ccadic/openDTU-Sulfuroid/finalbox3.JPG

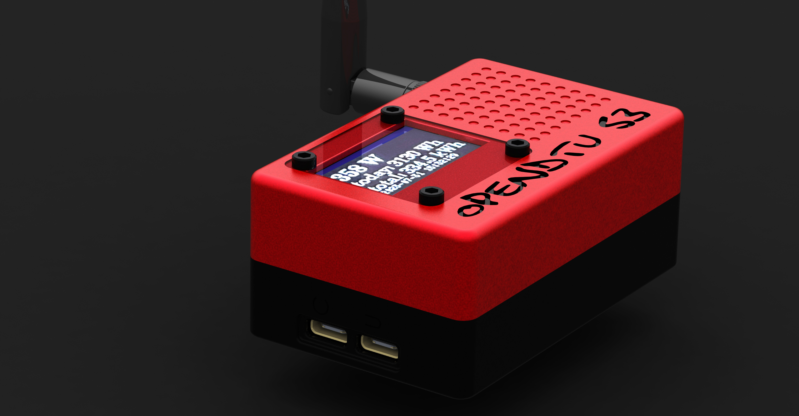
finalbox3.JPG
