ccadic/openDTU-Sulfuroid/finalbox4.JPG

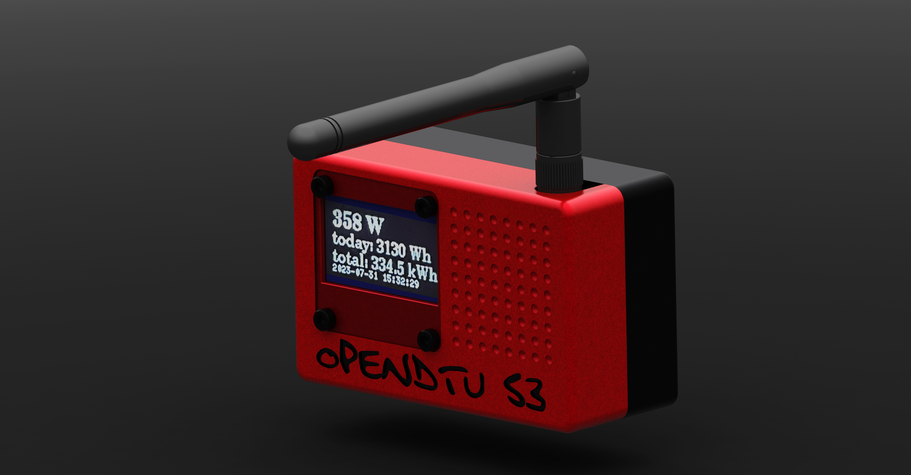
finalbox4.JPG
