ccadic/openDTU-Sulfuroid/openDTU3.jpg

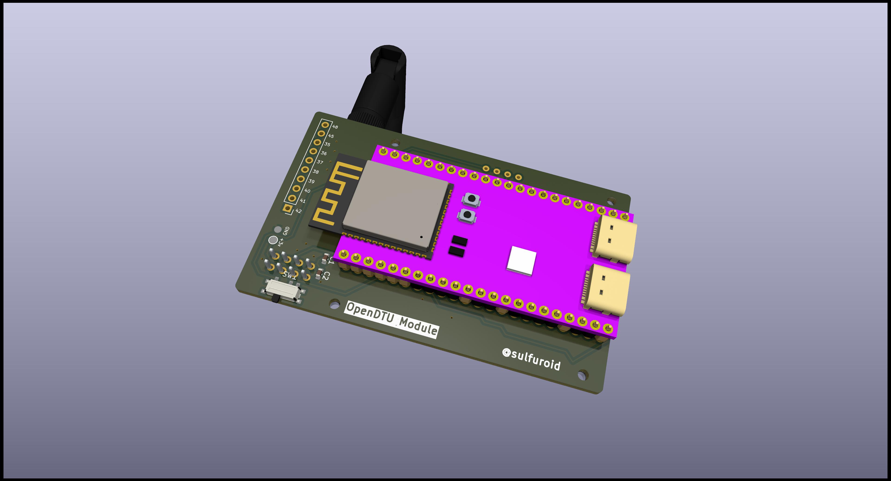
openDTU3.jpg
