ccadic/openDTU-Sulfuroid/openDTU.jpg

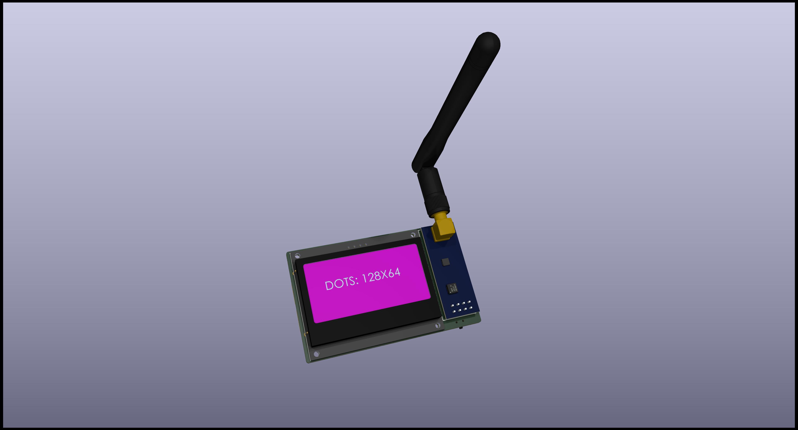
openDTU.jpg
