ccadic/openDTU-Sulfuroid/openDTUBIG6.JPG

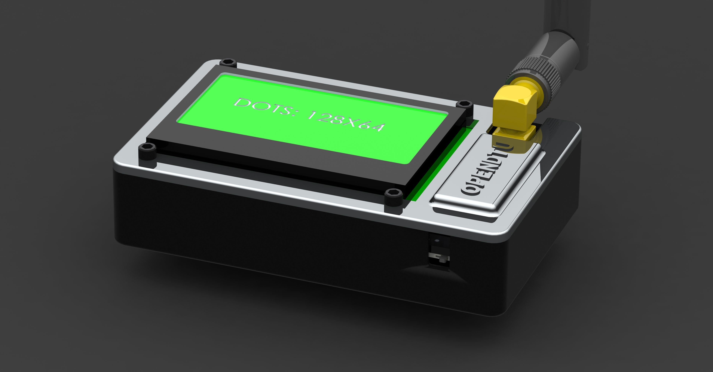
openDTUBIG6.JPG
