ccadic/openDTU-Sulfuroid/Untitled2.JPG

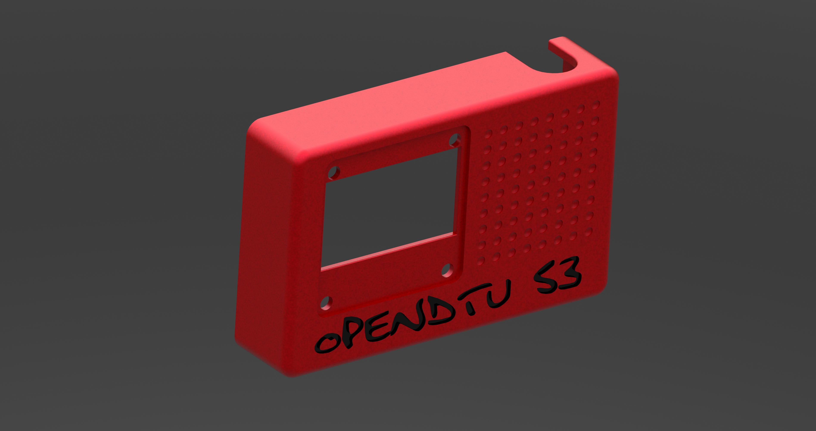
Untitled2.JPG
