ccadic/openDTU-Sulfuroid/Untitled.JPG

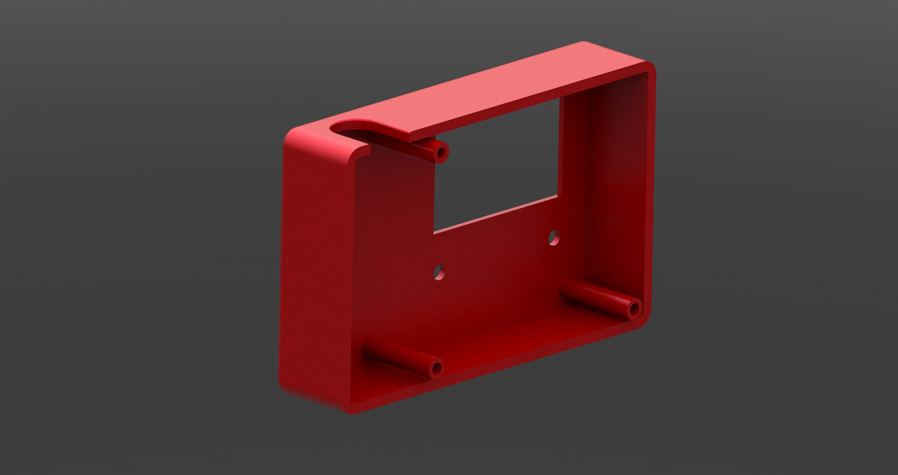
Untitled.JPG
